cezarbontas333/DisCuInv_PCB/sol_inv/res/WE-FLEX-749196521/749196521 (rev1).stp

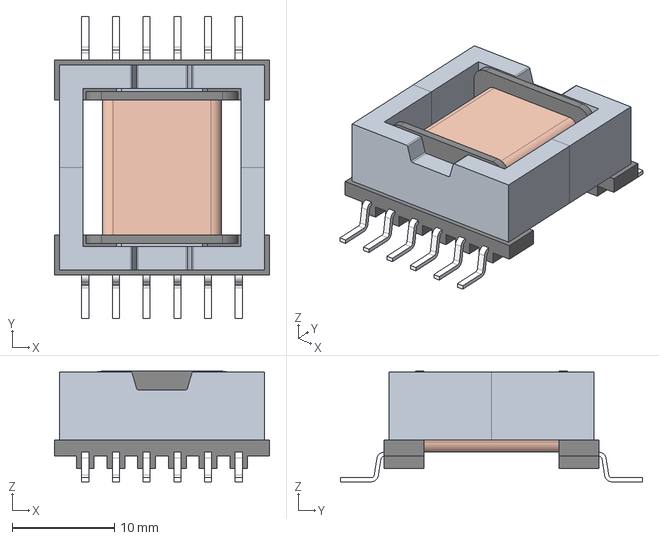
[picture p15: CAD file, 2025-04-09]
sol_inv/res/WE-FLEX-749196521/749196521 (rev1).stp
21.0 x 29.5 x 10.8 mm
